Yuxiaoyu2277/ESP32-S3-player/Firmware/ESP32_MP3_PLAYER/background.h

#define MIANBACKGROUND_HEIGHT 135
#define MIANBACKGROUND_WIDTH 240

// array size is 64800
static const uint16_t mianbackground[] PROGMEM  = {
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
};

#define MUSICBACKGROUND_HEIGHT 135
#define MUSICBACKGROUND_WIDTH 240
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
